Trasselfrisyr/MiniWI/Docs and references/casio-dh-recorder-fingering.png

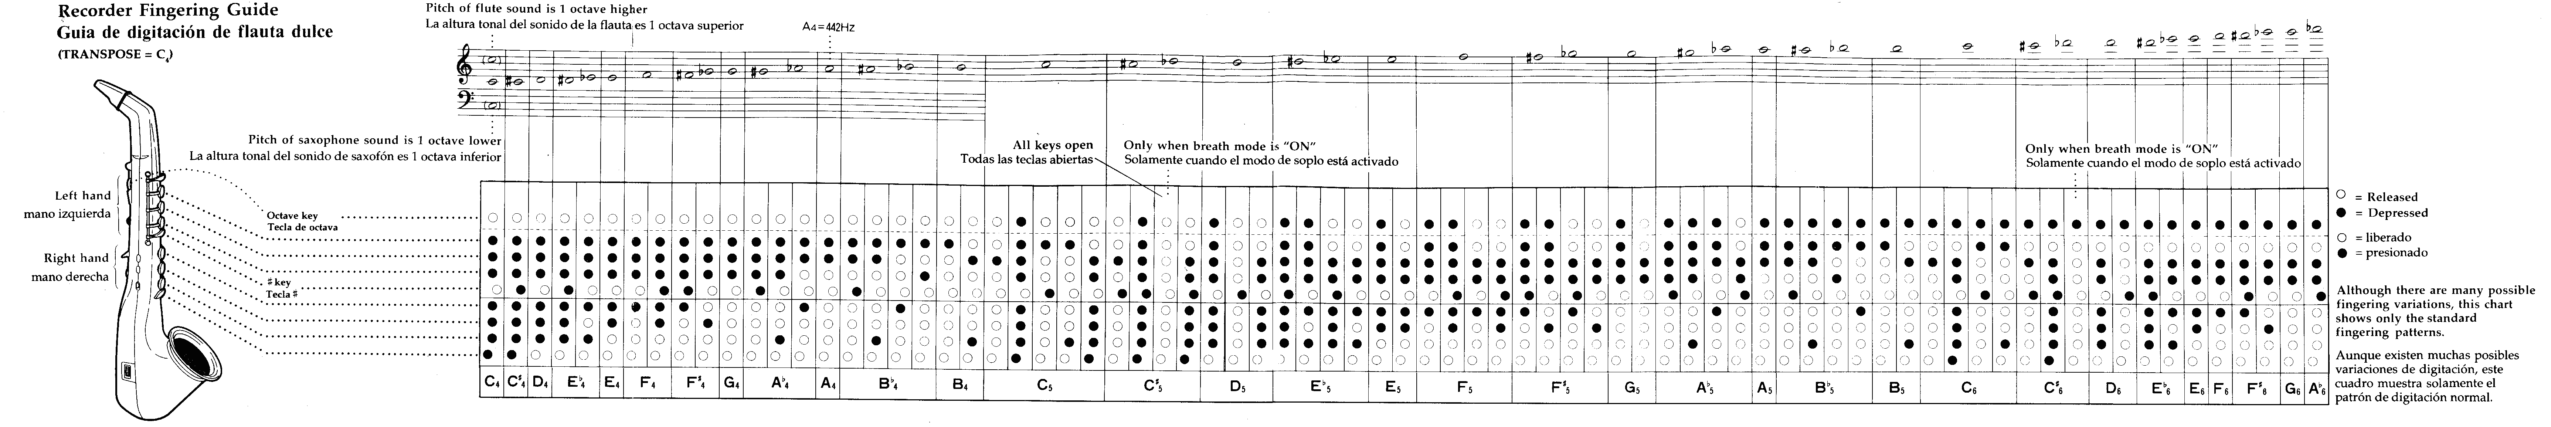
Docs and references/casio-dh-recorder-fingering.png
