Trasselfrisyr/MiniWI/MiniWI-cap-pmt/MiniWI-cap-pmt-fingering-casiomod.png

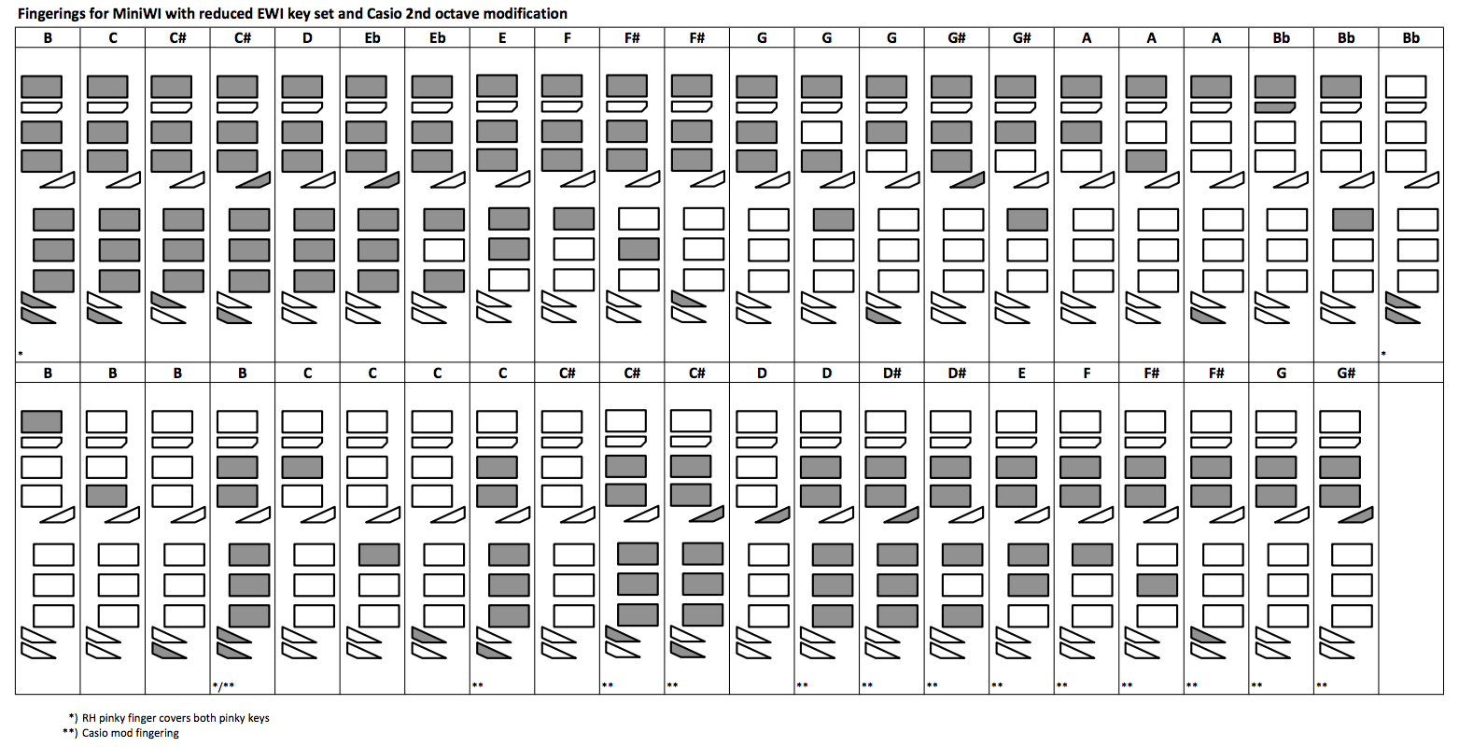
MiniWI-cap-pmt/MiniWI-cap-pmt-fingering-casiomod.png
