Trasselfrisyr/MiniWI/MiniWI-cap-pmt/MiniWI-cap-pmt-schematic.png

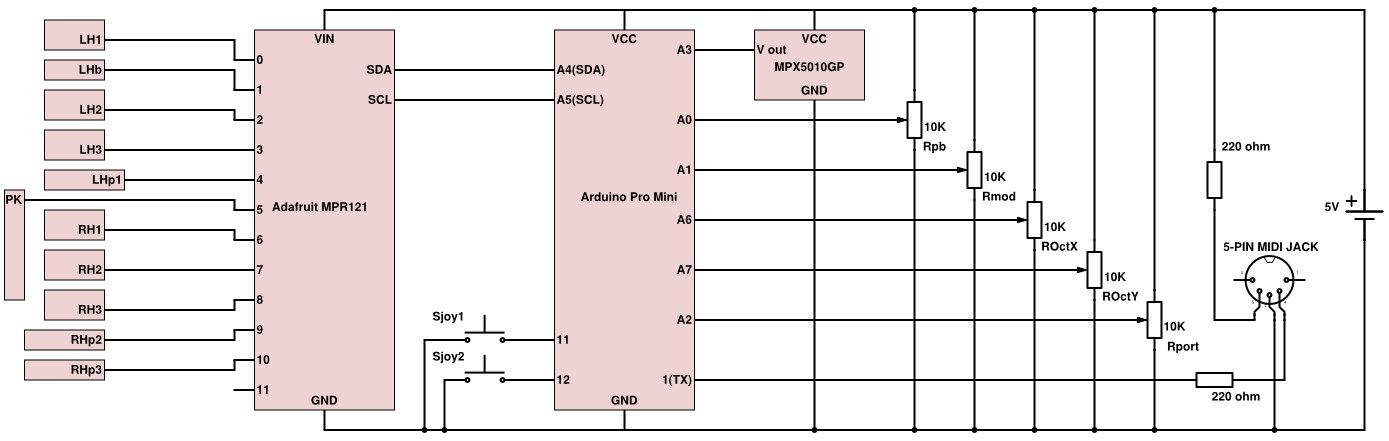
MiniWI-cap-pmt/MiniWI-cap-pmt-schematic.png
