Trasselfrisyr/MiniWI/MiniWI-cap-pmt/MiniWI-fingering-casiomod.png

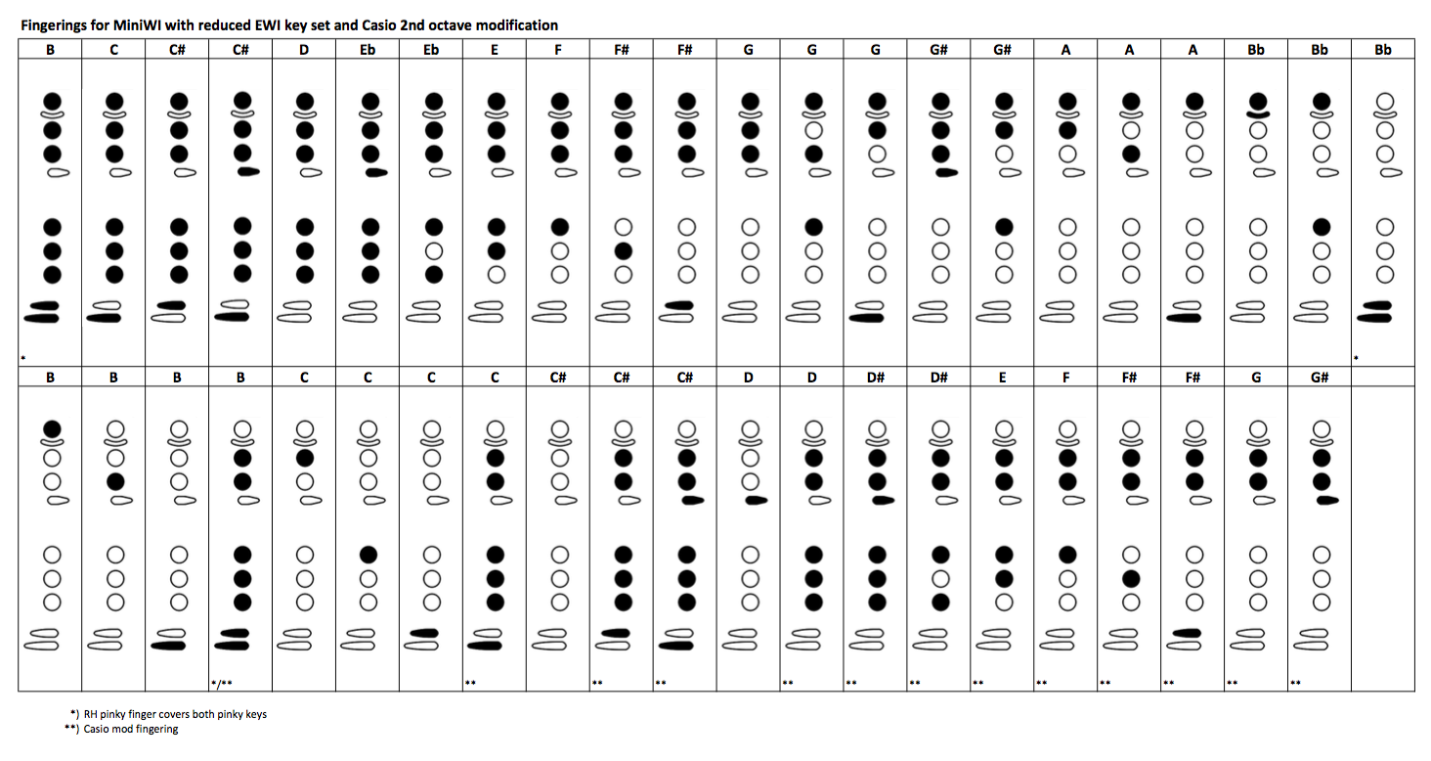
MiniWI-cap-pmt/MiniWI-fingering-casiomod.png
