Trasselfrisyr/MiniWI/MiniWI-cap-pmt/pmtver.png

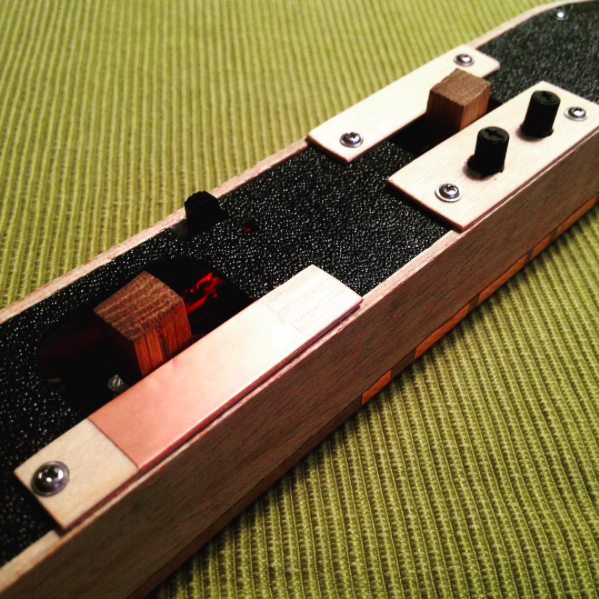
MiniWI-cap-pmt/pmtver.png
