Trasselfrisyr/MiniWI/MiniWI-cap/capverbottom.png

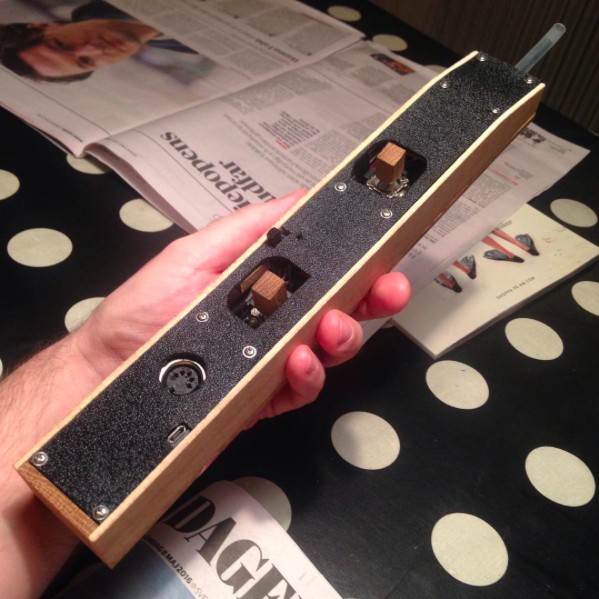
MiniWI-cap/capverbottom.png
