Trasselfrisyr/MiniWI/MiniWI-cap/capverinside.png

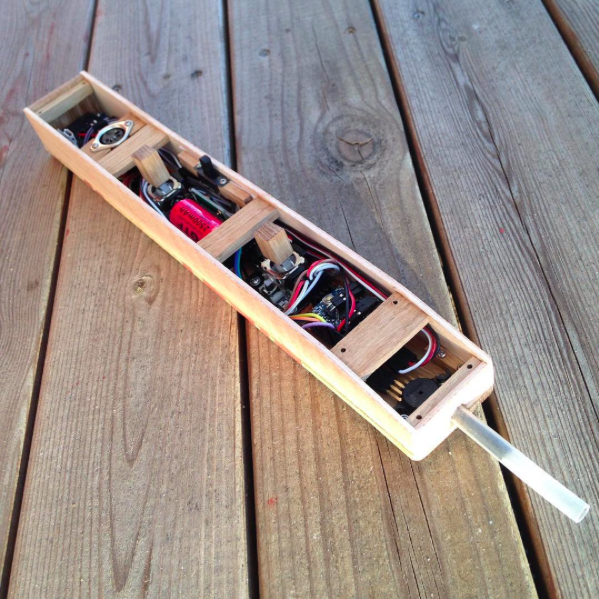
MiniWI-cap/capverinside.png
