Trasselfrisyr/MiniWI/MiniWI-cap/capvertop.png

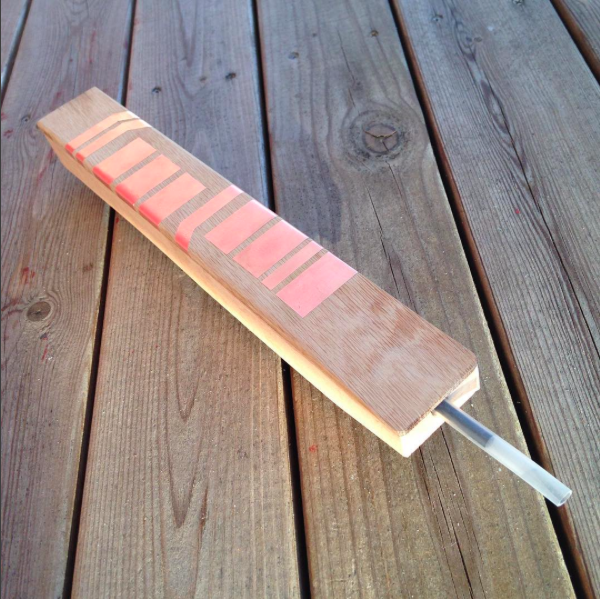
MiniWI-cap/capvertop.png
