Trasselfrisyr/MiniWI/MiniWI/miniwifirstproto.png

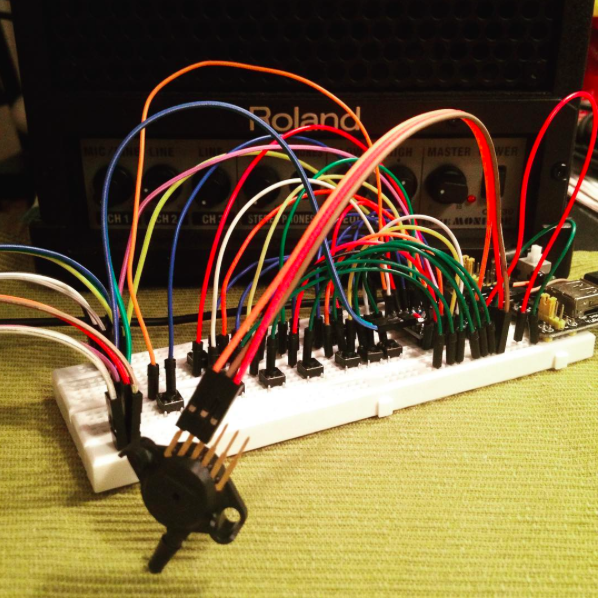
MiniWI/miniwifirstproto.png
