Trasselfrisyr/MiniWI/T.WI/curves.png

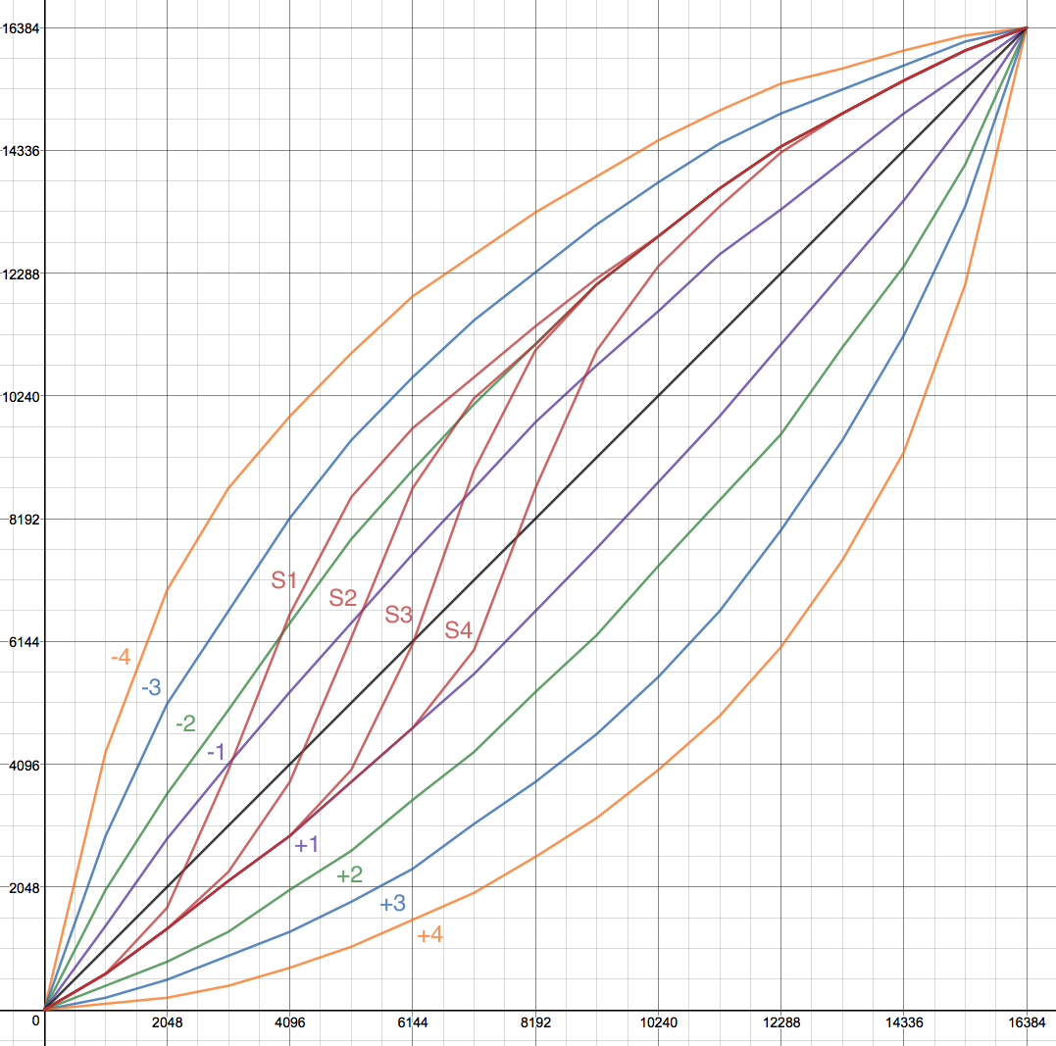
T.WI/curves.png
