Trasselfrisyr/MiniWI/T.WI/twi-joystick.png

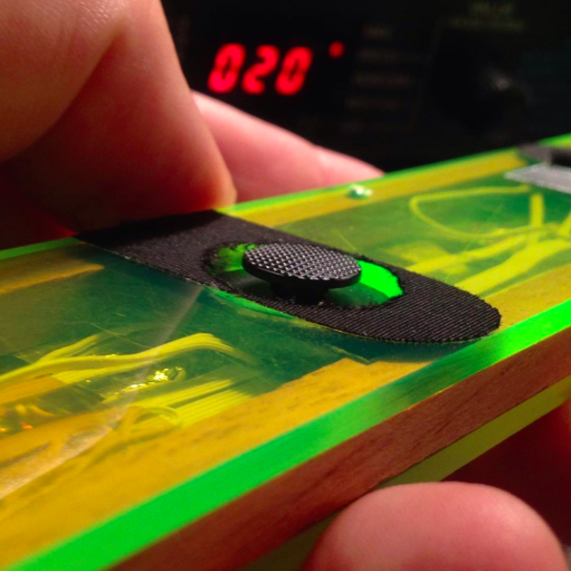
T.WI/twi-joystick.png
