Trasselfrisyr/MiniWI/TeensieWI/TeensieWI-fingering.png

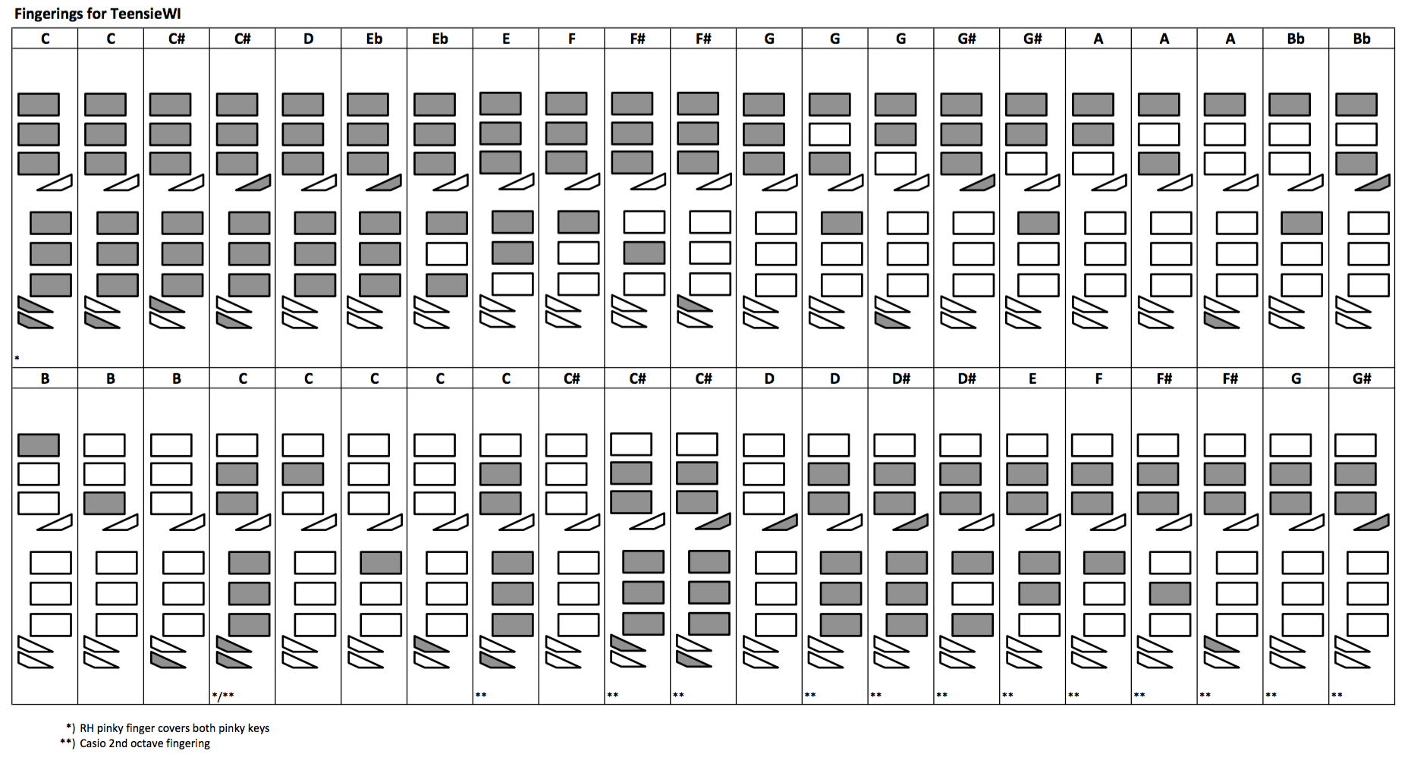
TeensieWI/TeensieWI-fingering.png
